H3wastooshort/BikeUSBv2/idea/voltage_limit_shitty_sim.asc

I1: current; 1A
Q1: pnp; 2SAR587D3
R1: res; 24k
R2: res; 130k
R3: res; 500
R4: res; {R_l}
R6: res; 0.1
U2: tl431
Named nets: V_shunt, V_in, 0, V_out
.dc I1 0mA 1000mA 1mA
.step dec param R_l 1 1000 2
