H3wastooshort/BikeUSBv2/firmware/BikeUSBv2/debug.h

enum debug_code_t {
  DBG_BOOT = 0,
  DBG_EEPROM = 1,
  DBG_RESET,
  DBG_LOOP,

  DBG_CONFIG = 31,
  DBG_CALIBRATE = 32,

  DBG_MSM_STATE = 64,
  DBG_SRC_STATE,

  DBG_FREQ = 96,
  DBG_AC,
  DBG_FREQ_METHOD,

  DBG_PDO = 128,
  DBG_PD_ERR,
  DBG_PD_MSG_IN,
  DBG_PD_DATA_OUT,
  DBG_PD_CTRL_OUT,
  DBG_POWER,

  DBG_FUSB_INT = 192,

  DBG_CRIT_ERROR = 255
};


template<typename T> void printDebug(debug_code_t code, T val);
void printDebug(debug_code_t code, void* val, size_t len);
