H3wastooshort/BikeUSBv2/firmware/BikeUSBv2/calibrate_mode.h

void calibration_setup() {
  printDebug(DBG_CALIBRATE, config.calibrate_mode);

  usr_led.setStatic(true);

  switch (config.calibrate_mode) {
    case 0:
      pwr_led.setPattern(cal_mode_pattern_2W5);
      break;
    case 1:
      pwr_led.setPattern(cal_mode_pattern_5W);
      break;
    case 2:
      pwr_led.setPattern(cal_mode_pattern_7W5);
      break;
    default:
      printDebug(DBG_CALIBRATE, 0xFF);
      config.calibrate_mode = 0;
      storeConfig();
      return;
      break;
  }

  digitalWrite(OUTPUT_ENABLE_PIN, HIGH);
}


void calibration_loop() {  //runs when in cal mode
  static uint32_t last_no_pg = 0;
  if (!isPowerGood()) last_no_pg = millis();

  if ((config.calibrate_mode > 0) && (last_no_pg != 0) && (millis() - last_no_pg > 5000)) {
    //save freq
    switch (config.calibrate_mode) {
      case 0:
        config.min_speed_2W5 = AC_frequency;
        break;
      case 1:
        config.min_speed_5W = AC_frequency;
        break;
      case 2:
        config.min_speed_7W5 = AC_frequency;
        break;
    }

    config.calibrate_mode = 0;  //make sure this only runs one
    storeConfig();

    //inform user to restart device
    usr_led.setPattern(cal_mode_pattern_done);
    pwr_led.setStatic(true);
    }
}
